avmolaei/AV-RK-MK2/img/1.png

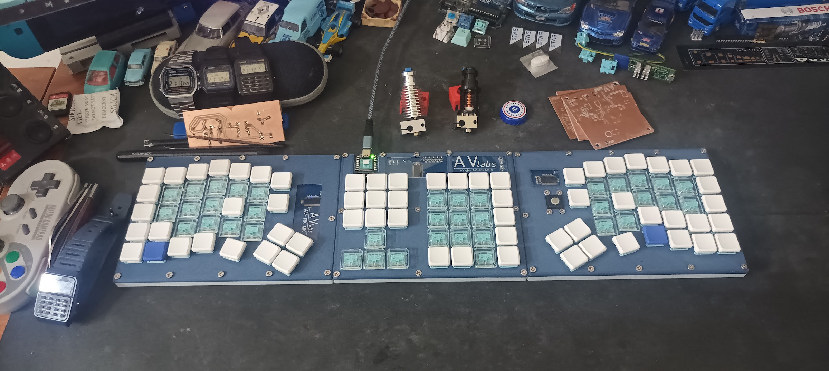
img/1.png
