avmolaei/AV-RK-MK2/AV-RK MK2 MODULE - SENSOR SCREEN/3D PRINTED PARTS/STL/BOTTOM.stl

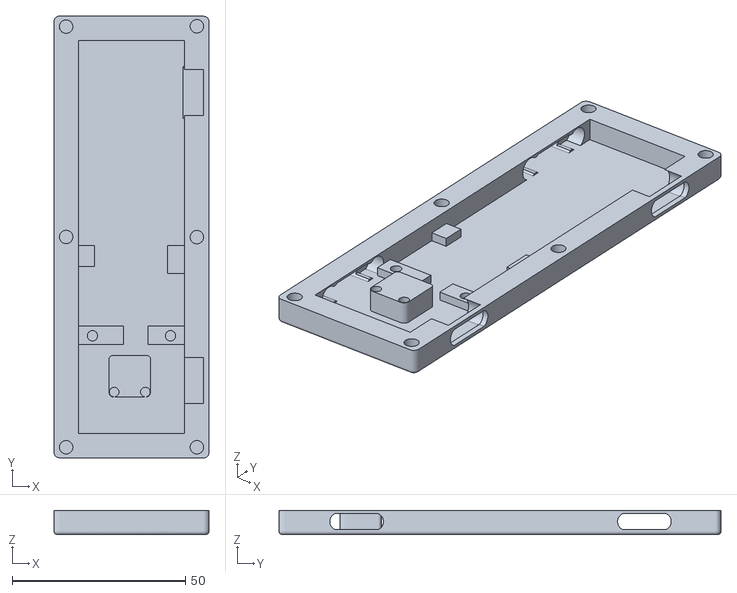
[picture p20: CAD file, 2023-08-15]
AV-RK MK2 MODULE - SENSOR SCREEN/3D PRINTED PARTS/STL/BOTTOM.stl
44.7 x 127.5 x 7.00
