avmolaei/AV-RK-MK2/AV-RK MK2 MODULE - MOUSE CHARGER/CAD FILES/top (2).stl

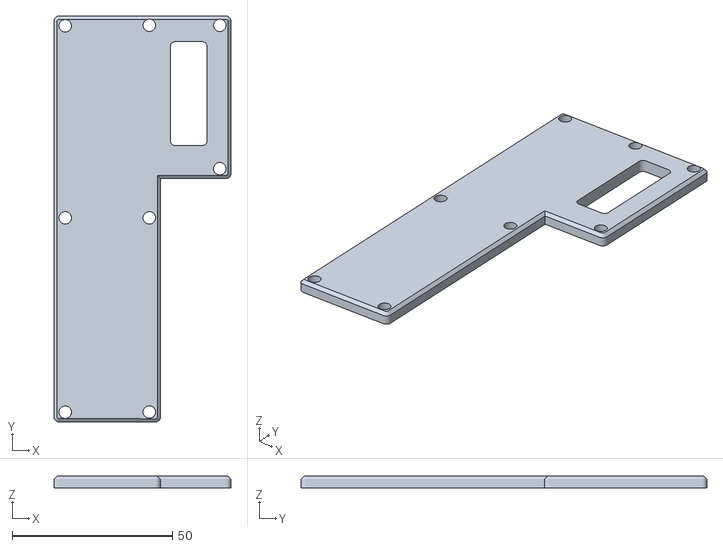
[picture p21: CAD file, 2023-08-10]
AV-RK MK2 MODULE - MOUSE CHARGER/CAD FILES/top (2).stl
55.2 x 126.7 x 3.80
